AuClark/rave-cave/docs/visuals.md

# Generative visuals

Code-driven visuals you can reshape live, in the spirit of Zach Lieberman's sketches. A **sketch** is a small GPU shader with named parameters. The `visuals` service on the brain holds their live values, and any projector surface set to **generative** shows the sketch, warped to fit that surface. Code: [`brain/visuals/`](../brain/visuals/). Service: `visuals` on the brain, port **8110**.

## Using it

1. Open **`http://sektor5.local:8110/`** on a phone or laptop (on Android, use the IP: `http://<brain IP>:8110/`).
2. Move the sliders. The preview and every generative surface update as you drag.
3. **Q**, **W** and **E** are the same dice at three energies — calm, groove, full on for the drop. **Randomise** throws everything, **Nudge** moves each value a little, **Reset** returns to the defaults. Each group has its own **random** button.
4. **Save** a look as a preset and **Load** it later. Presets are per sketch, and carry the ranges and automation as well as the values.
5. In the mapping editor (`:8100/edit`), set a surface's content to **generative** to put the sketch on it.

Everything is beat-locked: speeds are in cycles per beat, and **Beat punch** sets how hard each beat kicks the visual.

**Two pages.** The **Launchpad** (`:8110/pad.html`) is the phone one: pads for energy, effects,
presets and a desk section, with a launch-on-the-beat quantise. The **full controls** (`:8110/`) are
for rigging a look up. They share the same state over the same event stream, so one device can set
up while another plays. Both are described in **[visuals-live.md](visuals-live.md)**.

**Live** (`:8110/show.html`) is the remote for the night: the lights and the visuals on one page,
with the track that's playing above the picture. See **[show-app.md](show-app.md)**.

**Playing it live — [visuals-live.md](visuals-live.md).** Every parameter has a **range** (the orange
band on its track, with two ▲ arrows) that everything else respects, and an **automation** toggle that
moves it between the ends of that range on its own, in note values, locked to the beat. There are
keyboard shortcuts for the lot. That guide is the one to hand someone who is about to VJ; what
follows here is the reference.

### What the page stores

| | |
|---|---|
| Values | `GET`/`POST` `/api/params`, as before: `{id: value}` |
| Themes and Shuffle | `sketches/themes.json` groups the sketches (a sketch not listed shows under Other). `GET /api/sketches` returns `themes` and `titles` with the names. `GET`/`POST` `/api/shuffle`: `{on, theme, every, skip, queue, out}`; `queue` is `{sketch, preset}` (or null to clear) for the next change, `out` is one theme's `{theme, sketches, presets: {sketch: [...]}}` left out of Shuffle, replaced whole; `every` is 1, 2, 4, 8, 16 or 32 bars; `skip` changes on the next 1. It runs in `visuals.py` on showbrain's beat (a 120 BPM idle clock with no deck), hands over through the transitions below synced to the bar so the change lands on the 1, and is saved in `state/shuffle.json`. Picking a sketch or preset by hand restarts the period |
| Ranges and automation | `GET`/`POST` `/api/auto`: `{id: {on, lo, hi, rate, shape, phase, retrig, hz, duty}}`, plus `_freeze` on POST to hold every automation where it stands |
| Presets | `{"_v": 2, "values": {...}, "auto": {...}}`. A preset written before automation existed is a flat `{id: value}` and still loads, with automation off and ranges wide open. |

The automation itself is worked out in [`render.js`](../brain/projector/web/render.js) (`autoEval`),
once per frame, from `u_beat` — so it is frame-exact on the projector, identical on every surface,
costs nothing on the network, and needs no shader recompile. The control page reads the same numbers
back out of the renderer to draw its moving markers.

### Marking a parameter in the JSON

Three optional fields, so the page does not have to guess from names:

| Field | Meaning |
|---|---|
| `"kind": "rate"` | This is a speed. The page snaps it to note values (1/32 … 8/1, dotted and triplet) and shows it as one. Stored in cycles per beat as everywhere else; negative is backwards and 0 is stopped. |
| `"kind": "quality"` | This buys frame rate, not looks. Randomise and Q/W/E leave it alone. `cathedral`'s Steps is marked this way. |
| `"kind": "fixed"` | This is identity, not a setting, so the dice leave it alone too. Rolling it does not give you a different look — it gives you something that is no longer the thing it is meant to be. `hypnotoad`'s collar, keyline and tint are marked this way (a Hypnotoad with a randomised collar is just a frog), and so are `wormhole`'s Two tone and Mirror. Two tone is a choice between black-on-white and colour, and a value half way between the two collapses the contrast between the card and the ink; Mirror decides whether half the words come out mirror-image, and rolling it means three rolls in four give you backwards type. Both are look decisions rather than energies, and both are the thing that sketch exists to protect. |
| `"energy": 1 / -1 / 0` | Which way this parameter pushes for Q/W/E: 1 = more of it is busier, -1 = calmer, 0 = neither, so just randomise it. Without the field the page uses a list of the usual movers and settlers. |

## Sketches

| Sketch | Controls |
|---|---|
| `rings` | Structure: ring count, spacing, inner radius, zoom. Shape: sides (3–12) and roundness (polygon to circle). Wave: frequency, amplitude, phase per ring, speed. Motion: twist per ring, spin, beat punch. Line: width, glow. Colour: hue, hue spread across the rings, saturation, follow the show's colour. |

| `field` | Elements: density (dots across the surface height, up to 60), size, size variation, round to square, filled to outline. Movement: wander, wander speed, drift speed and direction (the whole field travels across the surface). Wave: a travelling wave that swells the dots (amount, frequency, speed, direction). Links: lines to neighbouring dots (a moving net), link width, glow. Colour: hue, spread, colour by random or by the wave, saturation, follow the show's colour. |
| `eye` | The all-seeing eye for the capstone. Eye: size, open, opens through the build, wide open on the drop, blink, white of the eye. Iris: size, rings, fibres, pupil, dilate with energy, look around and its speed. Around: rays, ray length and spin, the dollar-bill triangle, glow, line width. Colour, a paper background and thin lines shooting from the pupil. |
| `sacred` | Gold line geometry. Mode 0 Sierpinski triangle zooming forever into its apex, 1 Flower of Life, 2 Metatron's Cube (Fill 0 = circles only, cheaper), 3 golden spiral (Fill adds the counter-spiral), 4 pyramid tunnel (Fill twists it). Scale, detail, zoom in cycles per beat, spin, a pulse that runs through the levels, width, glow, colour. |
| `ascend` | Energy climbing a pyramid face. With Triangle on, it clips itself to the face (apex top middle), so a plain surface over a face needs no masks. Edge light, capstone glow, charge level (climbs through a BUILD, full on the DROP), rising bands, glyph rows and their scroll, colour. |
| `subliminal` | They Live-style words. Mode 0 flash each bar, 1 strobe each beat, 2 steady, 3 hidden behind a bland broadcast until the DROP. First word and how many (0-8 the obey set: OBEY, CONSUME ...; 9-15 the wake-up set: WAKE UP, THEY LIVE ...), random order, hold, size, black on white, background flash, RGB glitch, jitter, grain. |
| `cctv` | A surveillance camera: night vision, thermal or grey; figures walking; a targeting box that jumps to a new one every few beats with a label; REC, camera number, timestamp and beat counter; grain, scanlines, rolling bar, vignette, glitch and zoom punch on the kick. |
| `redacted` | A classified document: black bars slide off on the beat to show glowing hidden words (MAJESTIC 12, MK ULTRA, AREA 51 ...). All revealed on the DROP, blacked out in the OUTRO. Lines, margin, scroll, dark paper, how much is redacted and revealed, how often, a stamp that thumps down each bar. |
| `cipher` | A wall of scrambling code, style 0 pigpen (the Freemasons' cipher), 1 binary rain, 2 numbers station, with a message in the middle row that decodes letter by letter every few bars, follows a BUILD, and completes on the DROP. |
| `area51` | Mode 0 radar with a beat-locked sweep and blips (one moves wrong), 1 a saucer whose tractor beam grows through the build and blazes on the drop, 2 a glowing crop circle. |
| `reptile` | Iridescent hex scales rippling on the beat, with a slit-pupil eye that blinks and opens wide on the drop. |
| `seething` | A lumpy ball of living cells (after Andy Lomas's Seething video). Size, grows through the section, lumps; cells across, jitter, seethe speed; Folds carves brain-like creases; shading, background (black to white), colour. |
| `seed` | Neon branching trees over glowing flower dots (after Vincent Houze's Seed video). Trees, levels, branch angle and shrink, sway, grows a level at a time through the section; width, glow, blossoms, ground flowers, colour from trunk to tips. |
| `orb` | A black glass orb with a pearl circling inside on vintage paper (after Whiskas fx's Harmonisch Serie video). Size, wobble, pearl size, orbit, gloss; paper, mirror into four or tile, RGB split on the kick, pearl tint. |
| `pipes` | White square pipes in a grey tiled room (after Graphset's Echoes Reality video). Cells, pipe width, density, round to square corners, one or two drifting layers, re-roll every few bars, shadows, room tiles, tint. |
| `wavelength` | Lines made of waves. Mode 0 ridgeline (stacked waveforms, each hiding the ones behind, like Unknown Pleasures), 1 flowing sine lines, 2 an oscilloscope trace with harmonics. Lines, amplitude, frequency, detail, ridge width, speed in cycles per beat, phase per line, width, glow, colour or a rainbow in the colours of visible light. Presets: unknown-pleasures, ridge-spectrum, ridge-gold, spectrum, moire, scope, scope-rgb. |
| `track` | The waveform of the song actually playing, from the decks. Mode 0 terrain (Unknown Pleasures made of the song: each ridge is a bar, the front one playing now, the bars to come rolling in, so drops are visible before they land), 1 scrolling colour waveform past a playhead, 2 ring (the current stretch round a circle with a sweeping hand), 3 bass/mids/highs meters. Bars shown, beats shown, playhead, brightness of what has played, height, contrast, width, glow, the track's own colours or a tint. Presets: terrain, terrain-gold, terrain-white, scroll, scroll-show, ring, meters. |
| `sisyphus` | Khepri meets Camus: a dung beetle, head down and hind legs up on the ball the way real ones push, rolls the sun up a hill it never gets to the top of. It walks backwards in an alternating tripod gait, feet planted on each push, and lurches uphill one stride per A loop. On the last bar of every climb (the last two, for climbs of 16 bars or more) the sun teeters, gets away, bowls the beetle over and rolls back down, and the next climb starts on the phrase. **The sun lights the sky**, so every climb goes night (stars) to dawn to day and every fall is a crash back to dusk, over a far dune with two pyramids. The sun's face goes from resigned to straining to wide-eyed as it falls. **Hand** is the medium, and it is marked fixed so the dice never switch it: 0 wax crayon (strokes at different angles per surface, colour past the lines, paper tooth), 1 1930s rubber-hose ink (the default: brush line of varying weight, yellowed colour, flicker, grain, dust and pale film scratches), 2 acid (rotating sunburst, op-art contour stripes, posterised neon), 3 pencil flipbook (graphite hatching on cream paper, the sun the only colour, every drawing held for a quarter beat so the motion steps on the beat). The sketch carries its own `drive()` on a held clock so the flipbook can freeze frames. Hill: slope, bars per climb, size, stride. Sky: how dark the foot of the hill gets. Hand: style, bars per style (when cycling), boil, ink, fade to sepia. Then the three reactive slots ([reactive.md](reactive.md)): **A Hit** the strides, the shove into the ball and the dust, **B Move** the sun's rays (alternate rays swap length on the 8ths), sparkle and star twinkle, **C Change** the sky's colour swell. Presets: cuphead (close-up), crayon, flipbook, acid, cycle, long-haul (a 64-bar climb in sepia), night-shift (red sun, steep, a fall every 4 bars). |
| `emergence` | A Turing-pattern labyrinth after Maxime Causeret's video for Max Cooper's *Order From Chaos*. Pattern: complexity, stripe density, spots to worms to fill, solid blobs. Motion: slither (cycles per beat), rewire, spin, beat punch (fattens the worms). Organism: size, hole, ragged edge, grow through the song section. Colour: zone mixing, hue shift, saturation, follow the show's colour. |
| `flow` | Particles streaming through a noise flow field, leaving fading trails, after [Radiant](https://github.com/pbakaus/radiant)'s Flow Field with Particle Trails by Paul Bakaus (MIT). Field: detail, curl, evolve per beat. Particles: density, speed in heights per beat, trail length, line width, width and alpha variation, quality (trace steps: fewer is cheaper on the projector's GPU). Beat: punch (brighter, thicker on the kick) and push (the streams bend away from the centre on the kick). Colour: hue, spread, saturation, brightness, background, follow the show's colour. Presets: amber, mono, blue, rose, emerald, arctic (the original's colour schemes), illuminati-gold, storm. |
| `topo` | A topographic contour map of slowly evolving terrain, after [Radiant](https://github.com/pbakaus/radiant)'s Topographic Contour Map by Paul Bakaus (MIT). Every 5th contour is major, with elevation labels on a dark knockout. Terrain: hill size, relief, evolve per beat. Contours: levels, line width, glow, scroll (levels per beat, so the rings march up or down the hills). Beat: punch, a peak in the middle (negative for a crater), its radius, swell on the kick. Labels: chance, size, spacing. Colour: the original coral → amber → gold ramp or a tint (hue, spread low to high, saturation), brightness, background, vignette, follow the show's colour. Presets: amber, mono, blue, rose, emerald, arctic, pyramid-peak, rave-rings. |
| `pendulum` | Pendulum Wave, after [Radiant](https://github.com/pbakaus/radiant)'s Pendulum Wave by Paul Bakaus (MIT). Pendulum i swings (base + i) times per cycle, so they drift from a line through snakes and braids and fall back into line at the end of every cycle; the cycle is in beats, so the line comes back on the phrase (128 beats = 32 bars). Pendulums: count, cycle, swings per cycle for the longest, swing angle, trail in beats. Look: size, the curve through the bobs, pivot bar and guides. Beat: bobs flash on the kick, a ripple from the centre on each beat. Colour: the original amber → gold → coral or a tint (hue, spread left to right, saturation), brightness, background, follow the show's colour. Presets: amber, mono, blue, rose, emerald, arctic, phrase-gold (16-bar cycle), neon-swing. |
| `phyllotaxis` | Phyllotaxis Spiral, after [Radiant](https://github.com/pbakaus/radiant)'s Phyllotaxis Spiral by Paul Bakaus (MIT): a sunflower of glowing points, each a golden angle round from the last, with a faint Fibonacci lattice between neighbours. A pixel finds the few points that can touch it by solving for its place in the local Fibonacci lattice, so thousands of points cost only nine lookups. Spiral: points, spacing, grow from the centre over a cycle of beats (oldest points fade from the middle, everything fades before it restarts). Motion: spin, breathing (point sizes, along the spiral), tilt sway, a ripple outward on each beat. Look: point size and glow, lattice lines, centre glow, vignette. Beat: flash on the kick. Colour: the original amber → gold → coral along the spiral or a tint, brightness, background, follow the show's colour. Presets: amber, mono, blue, rose, emerald, arctic, golden-sunflower, vortex. |
| `sequin` | Sequin Wave, after [Radiant](https://github.com/pbakaus/radiant)'s Sequin Wave by Paul Bakaus (MIT): tiny mirror sequins on a hex grid, tilted by five interfering waves, flashing copper → gold → white as they catch the light. Ported nearly line for line (its reversed smoothsteps rewritten, since they're undefined in GLSL). Sequins: how many across, wave speed per beat, tilt, sparkle, individual shimmer. Beat: sparkle on the kick, a ring of flashes running out from the centre on each beat. Light: a roaming light (the original's mouse light) circling the surface, laps per 16 beats. Colour: the original gold or a tint, brightness, vignette, follow the show's colour. Presets: gold, silver, rose-gold, sapphire, emerald, disco-gold, dancefloor. |
| `gilt` | Gilt Mosaic, after [Radiant](https://github.com/pbakaus/radiant)'s Gilt Mosaic by Paul Bakaus (MIT): a Byzantine gold mosaic wall lit by three drifting candle lights, its tesserae turning over in a wave. Ported nearly line for line (reversed smoothsteps rewritten; its hash() is the renderer's). Mosaic: tiles per height, candlelight drift per beat, tile shimmer. Flip: wave on or off (off gives the still, shimmering wall), sweep and rest in beats (6 + 2 = one sweep every 2 bars), direction, a radial flip from the centre every N beats (the original's click). Beat: the gold flares on the kick. Colour: the original gold or a tint, brightness, vignette, follow the show's colour. Presets: byzantine, candlelit, silver-leaf, rose-gold, lapis, temple-drop, neon-temple. |
| `throne` | Golden Throne, after [Radiant](https://github.com/pbakaus/radiant)'s Golden Throne by Paul Bakaus (MIT): a golden sacred-geometry mandala of rings, petals, spokes, hexagons and triangles in counter-rotating layers, with golden-ratio spiral arms and fractal hex lace. Ported nearly line for line (reversed smoothsteps rewritten, and the original's spokes fixed: they drew dark rays through the mandala). Mandala: size, layers, spiral arms, lace. Motion: time per beat, layer rotation, whole spin. Beat: the lines glow and the centre flares on the kick. Colour: line glow, the original gold or a tint, brightness, follow the show's colour. Presets: golden-throne, cathedral, platinum, rose-window, lapis, ascension, portal. |
| `geometry` | Radiant Geometry, after [Radiant](https://github.com/pbakaus/radiant)'s Radiant Geometry by Paul Bakaus (MIT): golden sacred geometry that morphs from a tiled hex lattice of star rosettes to a single central mandala with petals, spiral arms and an ornate edge. Ported nearly line for line (reversed smoothsteps rewritten). Pattern: the morph (lattice → mandala), a swing toward the mandala over a cycle of beats, build through the song section (lattice early in a section, mandala by its end, so it forms through a BUILD), complexity (2 to 6 layers), size. Motion: time per beat, layer rotation, whole spin. Beat: the lines glow and the centre flares on the kick. Colour: line glow, the original gold or a tint, brightness, follow the show's colour. Presets: lattice, girih, mandala, breathing-temple (swings every 8 bars), build-to-mandala, platinum, neon-girih. |
| `tropical` | Tropical Heat, after [Radiant](https://github.com/pbakaus/radiant)'s Tropical Heat by Paul Bakaus (MIT): heat haze and chromatic aberration over flowing domain-warped noise in hot magenta, orange, amber and teal, with blooms of vivid colour. Ported nearly line for line (reversed smoothsteps rewritten). Heat: distortion, colour vibrancy, time per beat, zoom. Beat: the blooms flare on the kick; heat can follow the track's energy. Colour: hue shift, shift by the show's colour, brightness, vignette. Quality: octaves (the original's 6 is the heaviest sketch here) and chromatic mode: full samples the noise three times, once per colour channel, which is the original's fine, busy look; off (the default) samples once and shifts red and blue, a smoother liquid flow at about a third of the cost. Presets: tropical-heat (exactly the original), lite (cheapest), heatwave, lagoon, ultraviolet, carnival. |
| `eclipse` | A solar eclipse, played out: the moon crosses a limb-darkened sun over a cycle of beats, from a bite and a crescent through Baily's beads (sunlight through the valleys on the moon's limb) and the diamond ring into totality with the corona, chromosphere and pink prominences, then back out. The corona, solar wind, bloom and stars are from [Radiant](https://github.com/pbakaus/radiant)'s Eclipse Glow by Paul Bakaus (MIT; reversed smoothsteps rewritten, its hash renamed, stars and grain sized in output pixels). Eclipse: crossing in beats (0 = set the phase by hand; 0.5 is totality), how much of the cycle totality holds, totality as each song section ends (so a BUILD lands on totality), the moon's path angle, a miss (a partial eclipse), moon size (under 1 gives an annular ring of fire, with no corona), size. Sun: brightness, corona size, rays, prominences, lens streak, stars, corona time per beat. Beat: the corona and diamond ring flare on the kick; diamond strength. Colour: hue shift, shift by the show's colour, brightness. Presets: crossing, totality, diamond-ring, build-to-totality, ring-of-fire, partial, great-corona, blood-moon, black-sun. |
| `diamond` | Diamond Caustics, after [Radiant](https://github.com/pbakaus/radiant)'s Diamond Caustics by Paul Bakaus (MIT): prismatic fire through a brilliant-cut diamond, with caustic folds from faceted refraction, chromatic dispersion into rainbow fire, scintillating sparkles and star bursts. Ported nearly line for line (17 reversed smoothsteps rewritten, its hash and a local named refract renamed, float loops made int, and a seam in the original's dispersion fixed). Diamond: brilliance, fire (dispersion), sparkles, star bursts, zoom. Motion: time per beat, turning. Beat: sparkles and star bursts flash on the kick. Colour: hue shift, shift by the show's colour, brightness (default 0.55: the original's exposure washes out; the original-exposure preset has it). Heavy: about ten caustic lookups per pixel. Presets: brilliant, fire, ice, disco-diamond, sapphire, ruby, rave-rock, original-exposure. |
| `umbrella` | Rain on Umbrella, after [Radiant](https://github.com/pbakaus/radiant)'s Rain on Umbrella by Paul Bakaus (MIT): looking up through a rain-soaked umbrella at a blurred night city. The original simulates drops on a canvas every frame and hands them to a refraction shader; this is a stateless rebuild of the look: drops land (on the beat if you like), sit, then slide down the dome leaving trails of droplets, each one a lens onto a sharper, displaced piece of the city bokeh, with micro-droplets beading and drying between. The ribs, panels and hub are the original's shader code. Rain: amount, drop size, drop life in beats, slide, trails, micro-droplets, impacts on the beat. Look: refraction, city blur, city lights, walk (the city drifts past), umbrella ribs. Beat: the lights pulse on the kick. Colour: hue shift, shift by the show's colour, brightness. Presets: night-walk, downpour, drizzle, standing-still, neon-blue, rave-rain. |
| `artpop` | Artpop Iridescence, after [Radiant](https://github.com/pbakaus/radiant)'s Artpop Iridescence by Paul Bakaus (MIT): iridescent soap-film bubbles, thin-film rainbow bands over a domain-warped surface with fresnel edge glow and chrome highlights. Ported nearly line for line (reversed smoothsteps rewritten; the bubble edges' atan noise, which seamed at ±π, sampled round a circle instead; the small bubbles only computed where they are). Film: thickness (how many bands), flow per beat, warp (1 = the original, which folds the film into fine grain), size, small bubbles on or off, chrome highlights. Beat: the bands shimmer and the bubbles swell on the kick. Colour: band shift, shift by the show's colour, brightness. Quality: octaves (the original's 4 with full warp is about 190 noise lookups per pixel; the default 2 octaves at 0.4 warp is clean and about half that). Presets: holographic, original, lite, oil-slick, chrome-bubble, single-bubble, holo-pop. |
| `horizon` | Event Horizon, after [Radiant](https://github.com/pbakaus/radiant)'s Event Horizon by Paul Bakaus (MIT): a ray-traced Schwarzschild black hole. Each pixel follows its light ray's bent path (velocity-Verlet geodesics), crossing a Novikov-Thorne accretion disk with Doppler beaming and gravitational redshift, so the far side of the disk arcs over the shadow, with a photon ring and a lensed star field. Ported nearly line for line (its hash renamed). Black hole: zoom, disk brightness, chromatic (spectral rings), photon ring fringe, stars. Camera: orbit in turns per 64 beats, tilt (-0.2 gives the edge-on Interstellar view), roll, disk spin per beat. Beat: the disk flares and the photon ring pulses on the kick. Quality: step (1 = the original's up to 200 steps per pixel, the heaviest sketch here; the default 1.5 looks the same at two-thirds the cost). Presets: event-horizon, gargantua (original steps), lite, spectral, edge-on, from-above, singularity. |
| `burn` | Burning Film, after [Radiant](https://github.com/pbakaus/radiant)'s Burning Film by Paul Bakaus (MIT): celluloid catching fire in a projector. Burn holes open in dark film stock with a white-hot frontier and spread until it's all fire, embers glowing through, sparks drifting up, sprocket holes and grain; then it fades to black and a fresh strip starts. Ported nearly line for line (its many reversed smoothsteps rewritten, noise renamed, loop made int, grain sized in output pixels, and its sprocket holes, which came out as flat dashes, redrawn as real rounded holes). Burn: direction (spread, the default, or die down: the original's fire actually shrinks over its cycle, the opposite of what it describes), cycle in beats, burn through the song section (the film burns away over a BUILD, all fire by the drop), pattern drift, burn size. Fire: burning edge, ember glow, sparks. Film: sprocket holes, film run (the holes scroll through the gate, in holes per beat), grain. Beat: the frontier flares on the kick. Colour: hue shift, shift by the show's colour, brightness. Quality: octaves (6 = the original). Presets: burning-film, original, burn-the-build, fast-burn, slow-burn, blue-flame, toxic. |
| `vertigo` | Vertigo, after [Radiant](https://github.com/pbakaus/radiant)'s Vertigo by Paul Bakaus (MIT): an endless crimson tunnel of neon rings and segments, lit by waves of light running along it, with sparse ring flashes. Ported nearly line for line (reversed smoothsteps rewritten; its hash is the renderer's; its unused Spiral Intensity now twists the tunnel). Tunnel: speed in rings per beat, spiral, spin in turns per 64 beats, ring density, segments round. Light: wave speed, ring flashes, neon edges. Beat: the rings flash on the kick. Colour: hue shift, shift by the show's colour, brightness. Presets: vertigo, hyperdrive, spiral-down, ice-tunnel, acid, rave-tunnel. |
| `silk` | Silk Cascade, after [Radiant](https://github.com/pbakaus/radiant)'s Silk Cascade by Paul Bakaus (MIT): three layers of translucent silk in gold, rose and lavender, with domain-warped folds, Kajiya-Kay anisotropic sheen, backlit peaks and rare sparkles, drifting at different depths. Ported nearly line for line; the sheen's pinch points (where a fold flattens and its tangent is undefined) are faded out, and since the original's sheen is near full almost everywhere and washes the image out, sheen defaults to 0.7 with a contrast control (the original preset has both at 1). Silk: flow per beat, sheen, contrast, fold size, layers (1 to 3), sparkles. Light: the key light's orbit in turns per 64 beats. Beat: the sheen flashes on the kick. Colour: hue shift, shift by the show's colour, brightness. Presets: silk-cascade, original, emerald-silk, crimson-silk, single-sheet, disco-silk, show-silk. |
| `milking` | Alien Dairy: two greys milking a dancing cow under their saucer in a moonlit field, a cartoon drawn from 2D distance fields with ink outlines. The cow bobs, sways, stamps its legs in pairs, head-bops, swishes its tail and jingles its bell on the beat; the greys take turns, one squirt per beat, into a bucket that fills over a cycle of beats; the saucer's rim lights chase and its tractor beam flickers on the kick. Scene: dance, size, bucket fill in beats, ink line. Saucer: tractor beam, rim lights, beam hue, beam follows the show's colour. Night: stars, moon, brightness. Beat: the beam flares on the kick. Presets: moonlight-dairy, disco-dairy, slow-moo, red-alert. |
| `atlantis` | Atlantis Rising: Moses parts the sea and finds Atlantis, overrun by dolphins with thumbs. A cartoon drawn from 2D distance fields with ink outlines. The walls of water (foam, currents, spray) part over a cycle of beats, hold, then crash shut, or part through the song section so they're fully open by the drop; Moses raises his staff on every beat, its tip glowing; the temple, towers and crystal spire of Atlantis sit on the seabed, the crystal pulsing on the kick and throwing rays up between the walls; dolphins leap across the gap in their own lanes, each giving a thumbs up that pumps on the kick. The sea: part-and-close cycle in beats (0 = by hand), parted by hand, part through the section. Dolphins: how many, thumb size. Atlantis: crystal glow, light rays, glow hue, glow follows the show's colour. Look: size, ink line, brightness. Beat: the crystal and thumbs on the kick. Presets: parting, part-the-build, dolphin-party, red-sea-rave, exodus. |
| `wormhole` | **Your own words**, running round the inside of a pipe you are falling down. Type them on the Visuals page (or the pad's drawer) and separate them with `|`, up to eight. Two changes of coordinates stacked. Take the log of the radius and you get a distance that never runs out, so stepping it by whole numbers gives ring after identical ring with no end and no seam, and the angle is somewhere to run text along; travel and spin are then one term each, in cycles per beat, and every ring down to the vanishing point costs the same as the first. Before that the plane goes through a **Möbius transform**, `(z − a)/(1 − conj(a)·z)`, which maps circles to circles but moves the centre: the rings come out nested and not concentric, and the vanishing point sits off to one side at `a`. Because the map is conformal the letterforms stay letterforms, and its Jacobian keeps each ring's hairline one pixel wide. **It is lit.** How far down the pipe a ring sits drives the fog, so near words are bright and far ones sink into darkness towards a hot core at the vanishing point; the wall is a dark tint of the show hue and each word takes a hue either side of it (Follow is on by default, so Hue is an offset). Near letters have their edges sharpened back to a pixel, and far ones too small to read fade out instead of shimmering. **Two tone** (fixed) is the print version: black type on card, depth as haze, the pulse as a thickening hairline. **The sliders are scaled for reading, not for range**: every min and max is where the words still read, so a randomise, **Drop** included, gives a different tunnel and not an unreadable one. **Twist counts whole rings gained per turn**, and it has to be whole: `atan` has a branch cut at ±π, so a fractional twist makes the ring coordinate jump where the angle wraps and cuts the letters in half; it doubles as how many words are in the cycle. **Mirror** (fixed) folds the angle into wedges; half the words come out mirror-image, which is what a kaleidoscope does to type. Pipe: vanishing point off centre and its wander, rings per turn, times round, ring fill, travel, the kick's lurch, spin, twist, counter-creep, mirror. Type: seam hairline, weight, outline, Hectic (how much the hit brings in the streaks, chromatic split and bloom). Effects: those three always-on. Light and depth: fog (darkness gathering down the pipe), core glow, the kick's ring of light, hats glint, ribs, vignette. Then the three reactive slots ([reactive.md](reactive.md)): **A Hit** (every beat by default) lurches you down the pipe (forward only, beat-locked), fires a ring of light out of the hole and flares the core, **B Move** wanders the vanishing point and turns the pipe, **C Change** swaps the words and the palette. The hats glint the seams through their own `hats` amount, outside the slots, so kick, hats and chords each do something different without re-routing. Presets: hyperspace (a three-word spiral), kaleido, night-print, panter, read-me, strobe-words, event-horizon (warm, deep fog, a blazing core). None carries text, so they keep whatever words are typed. |
| `hypnotoad` | ALL GLORY TO THE HYPNOTOAD. Front-on and symmetrical in his own olive and cream whatever the show hue is doing (Tint overrules that), and **the eyes are the point**: bulging yellow eyeballs, shaded round with a glassy highlight and cupped by a lower lid, whose irises fill most of the eye and pour concentric bands of colour out of a small black pupil without stopping. The bands move in rings per beat with most of each beat's travel just after the kick; negative pours them inward. On the kick the iris widens and the pupil shrinks, a pale ring shoots outward through it and the eyes glow. Iris colour: 0 fire (pale yellow, orange, red, crimson), 1 rainbow, 2 the background's hue. The blink is an olive lid sweeping down. Behind him wavy hypno rings radiate from his eyes rather than the middle of the screen, on a small quantised palette with near-black dark bands (default violet, which makes the olive and the fire eyes pop), under **sacred geometry** with a soft glow, faded behind him so it frames him instead of crossing his face (0 Flower of Life, 1 Metatron's Cube, drawn from 11 lines by its hexagonal symmetry, 2 a ring-and-spoke mandala). **Caption** (fixed) puts ALL GLORY TO along the top and THE HYPNOTOAD along the bottom, meme-poster style, flashing on the kick, and he shrinks to fit between them. He is kept in frame: drawn big he crops at the feet, never the eyes. Toad: size, bob, blink, blotches, tint, collar, line weight (the last three fixed). Eyes: size, pupil, iris rings, how fast they pour, iris colour, caption. Then the three reactive slots ([reactive.md](reactive.md)): **A Hit** the bob and the eyes, **B Move** the geometry turning and the rings wobbling, **C Change** the palette and the line-work. Presets: glory (caption on), obey, stare, strobe-toad, swamp, temple, inward (rings pouring inward, rainbow irises). |
| `labyrinth` | A first-person walk through a maze that never ends, and it gives hope. You step a cell a beat (lurching on the kick, with a footfall dip and sway) and turn on the downbeat, the head easing into each corner. **The route is a pure function of the beat** and can never cross itself: it only ever gains ground one way, as straights and one-cell jogs with closed forms, so there is no state and every projector draws the same frame. The walls come from the route plus hashed side openings, alcoves, dead ends and colonnaded halls, and the route is never shut. **Drawn by an exact grid walk through the cells**, floor and roof as planes and encounters as analytic shapes, with no marching; on SwiftShader every branch runs, so the worlds are data rather than branches and each pixel draws one encounter. **Hope** is the subject: a lamp always waits round the next corner, growing and throwing rays down the corridor as you approach, then moving on as you take the turn; Ariadne's thread glows down the floor and round every corner with a bead of light running ahead on the kick; fireflies drift towards the light; and at the end of every phrase the roof slides open a panel at a time, light pours down in columns, and it closes on the next downbeat (it also opens on a drop). **Encounters** every few bars, seen coming down the straight and reached on a downbeat: glowing mushrooms you eat (a bloom, a shockwave down the corridor, then the maze trips for a phrase), a lantern, an orb, a door of light, a portcullis that lifts on the kicks, a curtain of threads, a fallen pillar. **World** (fixed): 0 hedge maze at dusk, 1 torchlit stone labyrinth, 2 neon grid under a synthwave sun, 3 ink on paper, 4 the mushroom trip. Walk: pace, bars per turn, lurch, bob, sway, field of view. Maze: world, branching, wall height, thickness, texture. Hope: the light ahead, thread, fireflies, fog, sky, how often the roof opens. Encounters: how often, which kinds (anything, mushrooms, lights, obstacles, lights and obstacles), how hard the trip. Render: steps and depth (frame-rate knobs). Then the three reactive slots ([reactive.md](reactive.md)): **A Hit** the footfall and the lamps, thread and fireflies flaring, **B Move** firefly sparkle, torch flicker, thread sway and a glance aside, **C Change** the light ahead swelling and the palette. Presets: minotaur, long-way-home, catacomb (stone), dusk-garden, magic-mushrooms (hedge), gridrunner (neon), sketchbook (paper), the-trip. |
| `mouths` | One huge mouth fills the screen and acts: fourteen exaggerated emotions (grin, smirk, a sinister Cheshire grin, a yell down to the uvula, a belly laugh, a gasp, a grimace, a pout, tongue out, a lip bite, a snarl over one canine, belting, a nervous anime wobble, and **bass face**). **A rig, not drawings**: every emotion is 24 numbers (open, width, each corner up or down, sneer each side, which teeth and gums show, clench, tongue, pout, lip bite, menace...), and the mouth springs from one to the next with overshoot and a stretch while it moves, starting just before the 1, so it never cuts. The lips are four curves across the width; the teeth are individual, with gaps, canines and gum scallops; the inside has a throat, uvula and a grooved tongue. **Bass face is tied to the track**: it fires hardest when the bass comes back in (how hard the kick lands at the beat onsets now against eight beats ago, calibrated on a real rekordbox waveform: onsets about 0.73 through heavy sections, 0.26 in breakdowns), simmers while it stays heavy, and takes over on the drop; the jaw pump turns into a head nod under it. Dancing: the jaw drops on the kick, the opening follows the mids, and the hats flick consonant shapes (M, F, O, E) on the 8ths. **Style** (fixed): 0 anime (clean line, cel shading, a fang, sweat drops and anger marks), 1 cartoon (thick ink), 2 detailed (shaded enamel, gums, a wet tongue, saliva strings), 3 pop art (halftone). Mouth: size, exaggeration, elastic, face hints, fang. Emotion: how often it changes (or hold one), which, mood (a family of emotions: happy, gremlin, cheeky, diva, anime chaos, sinister, stank), bass, drop. Dance: pump, sync, talk, bob. Style: style, ink, gloss, spit. Background: burst, halftone, speed lines, flat pulse or the style's own, and how busy. Then the three reactive slots ([reactive.md](reactive.md)). Presets: gremlin, diva, stank (mostly bass face), anime-chaos, pop-art, cheshire (slow and sinister), cheeky. |
| `inkwell` | Rubber-hose cartoons, after Fleischer, early Disney and Cuphead, climbing up out of an ink pool down a log-polar tunnel, or dancing in a row along a stage. Twelve subjects (a mascot critter, teapot, tree, flower, alarm clock, toadstool, cactus, ice cream, bomb, 1930s radio, candle, ghost) on **one shared rig**: pie-cut eyes and quick blinks, a grin that opens on the kick, noodle arms in white four-finger gloves, noodle legs down to big round shoes. **The feet stay planted and the body bobs over them**, so the legs bow like rubber; it squashes wide on the beat (harder on a loud kick), stretches on the way up, and rocks and shimmies a step behind its neighbour, with arm poses (charleston, hands up, elbows out) changing every 4 bars. The ink is thick and scales with the character, with a finer pen for faces and gloves, and **boils** four times a beat; halftone shades the side away from the light. The bodies are **masks** filled with a pattern drawn in their own coordinates, so it travels and squashes with the shape: 0 checkers, 1 candy stripes spiralling in, 2 polka dots, 3 op rings. **Colour is one of eight designed palettes**, each with its own card, floor, three fills, pattern and limb colour: 0 inkwell, 1 sunday comic, 2 silent, 3 neon, 4 two-strip, 5 hellfire, 6 seaside, 7 acid. Hue rotates the palette, Spread says how often a character reshuffles which colour goes where, and a continuous rainbow is deliberately not on offer: it is the single thing that makes work like this read as a screensaver. **Layout** 1 is the tunnel: every ring is a floor with an ink line under the feet and the wedges alternate colour, and Spin and Zoom are one term each (negative Zoom climbs out of the pool). Layout 0 is a chorus line on a stage, in front of a title-card sunburst. Small characters far down the tunnel drop fingers, props and faces, which is most of why it got cheaper. Cast: layout, how many, bars per subject, size, bounce, dance, how many get limbs. Movement: spin, zoom. Pen: line, boil, noodle. Fill: amount, pattern, scale, travel, halftone. Faces and props: strength, how many, how much C brings them in. Scene: background tint, rosette, background, film. Then the three reactive slots ([reactive.md](reactive.md)): **A Hit** the bounce, squash, eyes and mouths (and the candle flame, radio speaker and bomb spark), **B Move** noodling hoses, wiggling fingers and blinks, **C Change** the fills swelling and turning and who the cast reaches for next. Presets: tunnel, sunday-comic (row, polka dots, heavy halftone), silent (row, greys, heavy film), chorus (row, two-strip), deep (neon, op rings), warp (hellfire, deliberately chaotic), they-blink (acid, the faces arrive on the chords). |
| `cathedral` | A gothic nave you fly down and never reach the end of. Built from simple shapes so the architecture reads: a polished marble floor, fluted clustered piers rising into a pointed rib vault (diagonal and ridge ribs), pointed arcades opening onto dark side aisles with their own glowing windows, stone laid in visible courses, and above the arcade a great window in every bay whose **tracery is the fractal**: each arch holds two smaller arches and a round window, and each of those the same again, mirrored about the centre line, which is how real gothic windows are drawn. **Light is the subject**: a rose window at the far end throws beams back down the nave, sun shafts slant through the left-hand glass and pool on the floor, and the haze brightens towards the window so distance glows rather than going murky, with the near stone dark against it (projectors wash out mid-darks). The glass follows the show hue (Hue is an offset; Spread sets how many colours). **Raymarched**: the floor is hit exactly rather than marched, everything else is cheap to test per step, and the tracery, glass and rose are only worked out on the pixels that land on them. **Kaleidoscope** (`kal`, 0 = off, the default) folds the screen angle into mirrored wedges before the march, so neighbouring wedges meet in reflection, never a jump, and Roll turns the building inside them like a real kaleidoscope; narrow wedges are turned towards the side windows so each always holds glass. Structure: rose petals, tracery generations, tracery scale, form, fold, nave width, height. Flight: beats per bay, the kick's surge forward, the nave winding side to side (Twist; a true corkscrew would break the exact floor), roll, sway, kaleidoscope. Render: steps (the one frame-rate knob), depth, haze, shafts and beams, rose size, shading. Then the three reactive slots ([reactive.md](reactive.md)): **A Hit** surges you forward (continuous, never jumping back) and flares the rose, haze, glass and shafts with a wave of light up the nave, **B Move** makes the glass glitter pane by pane, **C Change** turns the glass palette and breathes the tracery's round windows. Presets: plain nave: nave, gold-vault, rose-window, cavern (a low, wide, red crypt), strobe-hall, lean; kaleidoscope: crystal (six-point star tunnel), hyperdrive (three wedges, fast, winding, rolling), rose-kaleido (twin rose windows in an eye). |

Low sides with no roundness, zero wave frequency and some twist gives the stacked, rotating-polygon spirograph look. High frequency with small amplitude gives rippling contour lines. In `field`, turning up Links with some Wander gives a drifting net; Wave with no Wander gives a clean grid of dots swelling in bands. In `emergence`, a large Size with no Hole fills the surface with maze (good for walls), and low Spots → worms gives cells instead of worms.

`emergence` is not a real reaction-diffusion simulation (that needs a feedback buffer the renderer doesn't have yet). It adds up plane waves of one wavelength in scattered directions and colours where the sum is above a level, which gives the same labyrinth with no memory between frames, so every surface stays in sync.

### Parameters that can empty the picture

The rule is that nothing may ever blank the screen, and the ranges are always clamped to each
parameter's own min and max, so automation cannot take a value somewhere the sketch does not allow.
Within that, these are the ones to be careful of when setting a range by hand:

| Sketch | Parameter | At its extreme |
|---|---|---|
| any reactive | `aamt` `bamt` `camt` at 0 | Not blank, but nothing reacts — the picture goes static |
| `cathedral` | `far` at its lowest | The nave ends in haze sooner; the near bays and their glass still draw |
| `cathedral` | `fog`, `glow`, `shade`, `sat` all at their lowest | The darkest it goes: flat stone, but the glass still reads clearly |
| `inkwell` | `bg` at 0 | The card goes black; the cast still draws, so it reads rather than disappears |
| `inkwell` | `size` at its lowest | The cast shrinks towards specks |
| `inkwell` | `pat` 0 **and** `face` 0 | Legal and fine — flat colour shapes — but the least interesting thing the sketch does |
| `inkwell` | `bg` 1 on a light palette | The card washes to near-white; the characters still read |
| `wormhole` | `fog` at its highest | The far rings sink into darkness sooner, but the near ones and the core always show. (Fog used to be an inverse radius, `0.07 / fog`, which blanked the card at its low end; it is now plain depth, 0–1.) |
| `wormhole` | `rings` at its lowest with `reps` 1 | Huge letters, a half-word per ring; still legible, which is why the floor is 1.8 |
| `subliminal` `redacted` | `bg` / paper values | Can go to solid black between flashes, which is the intent |

`cathedral`'s fold angle was the one real offender and is no longer reachable: the slider is mapped
onto the window that always builds something (see [reactive.md](reactive.md#gotcha-a-driver-must-not-be-able-to-empty-the-picture)).

### What the heavy sketches cost

Measured on the CPU rasteriser here (SwiftShader) at 1280×720 as a ratio to `rings`, medians of
interleaved runs on a busy machine. Only the ratios mean anything, and none of this was measured on
the projector's own GPU. After the rework:

| Sketch | vs `rings` | Before |
|---|---|---|
| `wormhole` | about 1.5× | 1.25× |
| `inkwell` | about 2.3× (`deep` 2.6×) | 2.9–4× |
| `hypnotoad` | about 2.3× | 2.2× |
| `sisyphus` | about 2.8× | 3.0× |
| `cathedral` | about 2.8× (`hyperdrive` 3.1×) | 5.9–6.6× |
| `labyrinth` | about 2.7× (`magic-mushrooms` 2.95×) | new |
| `mouths` | about 1.8× | new |

`cathedral` is the only sketch that raymarches, walking a ray through the scene for every pixel
where every other sketch answers each pixel with a formula. It halved when the 3D fold fractal
went: the floor is now hit exactly, the rest of the scene is cheap to test at each step, and the
glass is only worked out where it shows. **Steps** barely changes the cost any more (24, 48 and 96
are nearly the same); **Depth** shortens rays that hit nothing, and the sun shafts are about an
eighth of it. SwiftShader runs every branch, so the early-outs in `sisyphus` and `inkwell` show
nothing here and should pay on a real GPU. **Put the heavy ones on the rig and watch the fps on the
projector's stats before they go in a set.**

Each generative surface is drawn separately, so putting `cathedral` on two surfaces costs twice,
and the Stage page draws it again on top of the projector's own copy.

## Transitions

Changing the sketch, or loading a preset, hands over on the projector through a transition in time with the music, set in the **Transitions** section of the control page. The old sketch stays up until the sync point (now, or the next beat, bar or 4-bar phrase, or landing on the next drop), then the two play together for the transition's length in beats.

| Type | What it does |
|---|---|
| Auto (smart) | Picks one that suits the song section showbrain is in, never the same twice running: a flash cut, a stutter or a zoom into a PREDROP or DROP; a zoom, swirl, pixelate or tiles through a BUILD (1 bar); a dissolve, luma, crossfade or iris in a BREAKDOWN, INTRO or OUTRO (4 bars); a wipe, iris, tiles, slices, dissolve, pixelate or swirl in the groove. |
| Cut | An instant change on the sync point. |
| Crossfade | A straight fade. |
| Wipe | A soft line sweeps across at one of 8 angles, lit in the show's colour. |
| Iris | A glowing circle opens from the centre. |
| Dissolve | The new sketch burns through the old in noise-shaped holes with a hot edge. |
| Luma | The new sketch's bright parts appear first, then its darks. |
| Tiles | Squares pop in at random, each growing from its centre. |
| Glitch slices | Horizontal bands of the new sketch slide in from the sides. |
| Zoom through | The old sketch zooms in and away while the new one flies in from the centre as a framed picture. |
| Swirl | The old one twists away as the new one untwists in. |
| Stutter | The two flicker on 16th notes, the new one more and more, until it holds. |
| Flash cut | A white flash, with the cut on its peak. |
| Pixelate | The old one breaks into big pixels and the new one resolves out of them. |
| None | Instant, as before. |

Length is automatic (each type's own) or 1 beat to 8 bars. **Presets morph too** makes loading a preset transition from the old values to the new ones in the same sketch. **Mix to the next one** switches through the current transition to what Shuffle would pick next: Next up if something is queued, otherwise a sketch from Shuffle's theme with one of its presets, only from what is ticked in (see Themes and Shuffle). It works with Shuffle off. **Shuffle's own changes go through transitions too**: it sends each one inside the last beat of the bar with the sync forced to the bar, so every projector starts it exactly on the downbeat however late the message arrives, and the transition is never longer than Shuffle's period (an instant change becomes a cut on the 1). The API is `GET/POST /api/transition` (`type`, `beats`, `sync`, `presets`), `POST /api/next`, and `POST /api/select` takes an optional `"transition": {...}` to override the settings once (e.g. `{"type": "cut"}`).

How it's drawn: while a transition runs, each generative surface draws the outgoing sketch with its old values and then the incoming one on top, whose alpha is the transition's mask (in `render.js`, `COMMON`: `u_trole`, `u_tp`, `u_tmode`, and the `s5t_` functions). Either side can warp its own coordinates (zoom, swirl, pixelate, slices). There's no render-to-texture, so it runs on the projector's WebGL1 GPU, but for the transition's length the surface costs both sketches together: going between two heavy sketches (tropical, diamond, artpop, horizon) may stutter on the X3. Sketches need no changes.

## Climaxes on the drop

Timeline sketches have a best moment: eclipse's diamond ring into totality, atlantis's sea fully parted, burn's frame all fire, pendulum's bobs back in one line, geometry's full mandala, milking's full bucket, phyllotaxis's full bloom. Left alone, their cycles run on the beat count and the climax lands wherever it happens to. showbrain predicts the next drop from the track's analysis (`beats_to_drop`), so these sketches can aim for it: with **Land the climax on the drop** on (in their Beat group, on by default), the renderer eases the sketch's cycle, running it up to twice as fast or holding it, so the climax arrives on the drop's downbeat, getting there about a bar early. With no drop predicted (no rekordbox analysis, or none coming) the cycle runs on from wherever it is, so it never jumps. The kick and other beat animation stay on the real beat; only the cycle is moved.

A sketch opts in with a `climax` entry in its JSON: `{"cycle": the param holding its cycle length in beats, "peak": where the climax is in the cycle (0..1, or an expression of its params such as "0.5 - hold / 2"), "lock": the on/off param, "what": a description}`, and runs its cycle on `u_cbeat` instead of `u_beat` (see `MapRenderer._cbeat`). Sketches also get `u_todrop` (beats to the predicted drop, -1 when none) and `dropArc()` in the shared header: 0 far from a drop, rising to 1 over the 16 beats before one and easing off over the 8 after, for anything that should build into the drop.

Transitions can land on the drop too: set the Transitions sync to **Land on the next drop** and the change's cut (its end, or a flash cut's peak) falls on the drop's downbeat, shortened to fit if the drop is close; with no drop predicted it waits for the next bar. Auto does this by itself when the change comes in a BUILD, HOLD or PREDROP with a drop predicted within 16 bars.

## Writing a sketch

Add two files to `brain/visuals/sketches/`:

- **`NAME.glsl`**: declares `uniform float p_<id>;` for each parameter and defines `vec3 content(vec2 uv)`. `uv` is 0..1 across the surface. It can use everything the projector's shaders get: `u_beat`, `u_frac`, `kick()` (1 on the beat, decaying), `u_hue`, `u_energy`, `u_scene`, `u_aspect`, `hsv()`, `hash()`, `wave(beat)` (the live track's waveform, see below), and `drive()` with `band()`, `loopBeats()` and `barBeat()` (see [reactive.md](reactive.md)). See [`render.js`](../brain/projector/web/render.js) (`COMMON`).
- **`NAME.json`**: title, description and parameter groups, each parameter with `id`, `label`, `min`, `max`, `step` and `default`. The control page builds its sliders from this.

Deploy with `brain/deploy.sh visuals` and pick it in the Sketch card on the control page. If the shader doesn't compile, the control page shows the error and the projector keeps the last working sketch.

For sketches driven by the track's frequency bands on their own loop lengths — the kick punching on the beat, the hats in 8ths, the chords swelling over 8 bars — see [reactive.md](reactive.md). Every sketch already has `drive()`; `sisyphus` is the one built on it.

## Conspiracy set

Sketches and presets for the conspiracy-themed night (a pyramid with an eye on the capstone). Each theme is a sketch with several presets to try:

| Theme | Sketch | Presets |
|---|---|---|
| The all-seeing eye | `eye` | watcher, dollar, reveal (opens on the drop), hypnotic, void |
| Sacred geometry | `sacred` | sierpinski, sierpinski-prism, flower-of-life, metatron, golden-spiral, sunflower, pyramid-tunnel, twisted-tunnel |
| Energy rising up the pyramid | `ascend` | charge, hieroglyph-wall, power-lines, full-power, cold |
| Red-string board | `field` | string-board, string-web, evidence-wall |
| Ciphers | `cipher` | pigpen, matrix-rain, numbers-station, novus-ordo |
| CCTV | `cctv` | night-vision, thermal-hunt, grey-cam, motion-alarm |
| Subliminal messages | `subliminal` | obey-flash, they-live, wake-up-strobe, drop-reveal, watching |
| Hypnosis | `rings` | hypno-spiral, mkultra, op-art, crop-rings |
| Aliens | `area51` | radar, radar-red, tractor-beam, abduction, crop-circle, crop-gold |
| Redacted files | `redacted` | top-secret, dark-files, heavy-redaction, declassified |
| Reptilians | `reptile` | lizard, snake-eye, iridescent, dragon |

Several of these react to the song's sections: the eye opens and the pyramid charges through a BUILD, and the DROP gives the reveal (eye wide open, words shown, message decoded, files declassified). Without showbrain the idle clock never reaches a BUILD or DROP, so those presets look quiet when testing at home.

### Shipped presets

Presets in `sketches/presets/NAME/*.json` ship with the sketch in git and show in the preset list alongside the ones saved on the brain. A preset file only needs the values it changes; everything else takes the sketch's defaults. Saving a preset with the same name on the brain overrides the shipped one.

### Text in sketches

Shaders can't draw text by themselves, so `tools/glsltext.py` writes a 5x7 pixel font and a list of messages into a sketch. The sketch lists its messages on a `// @messages: OBEY|CONSUME|WAKE UP` line and has an empty `// <text>` ... `// </text>` block; running `python3 brain/visuals/tools/glsltext.py brain/visuals/sketches/subliminal.glsl` fills the block. To change the words, edit the `@messages` line and run it again. The block gives the shader `textCov()` (a message), `charCov()` (one character), `msgLen()`, `msgChar()` and `CH_A` ... `CH_9` for drawing live numbers. Letters, digits, space and `: - . ! ? / # '` only.

## Max Cooper set

Simplified takes on five Max Cooper videos, each a sketch with presets:

| Video (artist) | Sketch | Presets |
|---|---|---|
| Seething (Andy Lomas) | `seething` | seething-red, brain, grey-mass, pink-coral |
| Seed (Vincent Houze) | `seed` | neon-grove, coral-bloom, blue-sprout, golden |
| Third (Vicetto) | `eye` | third-blue, third-green, third-teal |
| Harmonisch Serie (Whiskas fx) | `orb` | harmonisch, black-pearl, mirror, rgb-tiles |
| Echoes Reality (Graphset) | `pipes` | echoes, maze, round, blue-steel |

`emergence` (Order From Chaos, Maxime Causeret) is the sixth.
## The live track's waveform

Sketches can draw the song that's playing. rekordbox analyses every track when the USB is prepared, the decks share that colour waveform over Pro DJ Link, and deckdash already fetches it with the beat grid (`/api/wavedetail/N`, `/api/timeline/N`). Nothing has to be uploaded per song; it works for any track loaded from rekordbox media.

- `trackwave.py` in the visuals service follows showbrain's live deck. When its track changes (deckdash's `waveformKey`), it fetches the waveform and beat grid and resamples the waveform onto the grid, 8 samples per beat, keeping the loudest frame in each slice. It pushes the result to every page once per track as a `wave` event: RGBA bytes (height, bass, mids, highs) in a 256-wide texture.
- `render.js` uploads it as a texture and gives every sketch `vec4 wave(float beat)`: height, bass, mids and highs (0..1) at any beat of the track, where 1 is the first beat. Sketches look it up with `u_beat`, so it stays on the beat through tempo changes and can read ahead (`wave(u_beat + 16.0)` is four bars from now). Outside the track it returns 0.
- The `track` sketch uses it (terrain, scroll, ring, meters).
- **At home** (no decks) it plays a demo track, looped. To test with a real track, capture one on the rig with a track loaded: `python3 brain/visuals/tools/capture_wave.py http://<brain IP>:8080`. That saves `brain/visuals/state/wave-sample.*` (not in git), which is then used, looped, whenever no deck is live.
- `GET /api/wave` returns the current waveform message (`source`: `live`, `sample` or `demo`; `title`, `beats`, `spb`, `w`, `h`, `data`).
## The words you type

Sketches can't draw type by themselves, so the page draws it for them. There is a **Words** field
on the Visuals page and in the pad's drawer: type a few words separated by `|` and every sketch
can read them immediately.

- The service holds one string (`GET`/`POST` `/api/text`, up to 240 characters, control characters
  stripped) and pushes a `text` event to every page and projector.
- [`render.js`](../brain/projector/web/render.js) `setText()` splits it on `|` or a newline, takes
  the first eight words, and draws each into one row of a 2048×2048 eight-row atlas — each word
  scaled down to fit its row so the letterforms keep their proportions however long the word is.
  Drawn once per change on the CPU, uploaded as one texture. 2048 gives each row 256 pixels of
  height, which sounds generous until a sketch magnifies one row over half the screen: `wormhole`'s
  nearest ring does exactly that, and at 128 the diagonals of the letterforms stair-stepped.
- Every sketch gets `uniform sampler2D u_text`, `uniform float u_textn` (how many rows are in
  use) and the helper **`float word(vec2 uv, float row)`** in `COMMON`: coverage of word `row`
  at `uv`, where `uv` is 0..1 across that word's own row and `uv.y = 0` is the top of it. Off the
  edge of the word it returns 0, so a sketch can lay type anywhere without clipping it.
- The words are saved with the live values and go into presets, so a preset can carry its own
  message. `wormhole` is built on this; `subliminal`, `redacted` and `cipher` still use the older
  baked 5×7 font (`tools/glsltext.py`), which is compiled in and not editable live.

## Reaction-diffusion lab

**`http://sektor5.local:8110/rd.html`** (on Android, use the IP) is a standalone test page running a real Gray-Scott reaction-diffusion simulation on the GPU, after [Karl Sims](https://www.karlsims.com/rd.html). It is not a sketch: it's there to find looks and to check what the projector's GPU can handle before simulations go into the shared renderer.

- Pattern buttons set feed and kill (Coral, Mitosis, Mazes, Fingerprint, Worms, U-skate and more) and reseed. Draw with a finger or the mouse to add chemical.
- **Pattern map**: Uniform, Karl's f/k map (every behaviour at once), or Radial (your pattern in the middle, spots at the rim).
- Speed is in simulation steps per beat, so growth follows the tempo. **Seeds on beat** drops new growth on each beat (a burst on DROP); **Feed pulse** makes the pattern breathe with the kick. Beat comes from showbrain via `/api/events`, with a 120 BPM idle clock without it.
- The stats show fps, simulation size, and the storage the GPU supports (float32, float16, or an 8-bit packed fallback that works everywhere). If the fps drops, lower the resolution.
- URL options for bookmarking a look: `?preset=mazes&look=1&res=4&mode=2&speed=200&seeds=0.3&pulse=0&hud=0` (also `f=` and `k=`). **H** hides the panel.

## How it works

- `visuals.py` serves the control page, the sketch (`/api/sketch`) and its values (`/api/params`). It pushes `sketch` and `params` messages to every open page over Server-Sent Events (`/api/events`), plus showbrain's state for the preview's beat clock.
- The projector page and the mapping editor also connect to `:8110/api/events`. The renderer compiles the sketch as content `gen` and sets its `p_*` uniforms every frame, so slider moves need no recompile.
- The control page's preview is the projector's own renderer (`/render.js`, served from `../projector/web/`), so it shows exactly what the projector draws.
- The beat clock runs smoothly at the track's tempo and eases towards the show engine's reported position (at most 10% faster or slower), so network jitter on the ~20 updates a second doesn't show as stutter. It only jumps on a seek or track change.
- Shaders get `u_px` (one output pixel in surface units), so lines never go thinner than a pixel and don't shimmer as they move.
- Live values and presets are kept on the brain in `~/visuals/state/`, not in git.

## Speed

- **Compression and caching.** The visuals and projector services gzip what they send when the browser asks (pages and three.js shrink 3–4×, the venue 3×, and the Stage's light-frames stream 16×, each message still sent at once; the small event streams stay plain), and give every static file an ETag, so a browser that already has a file gets a 304 and no body. deckdash's HTTPS proxy passes neither header on, so it gets plain responses as before.
- **Adaptive resolution.** The previews (Visuals page, Live, the Launchpad, the Projection editor) draw at no more than 2× the screen's pixels, and `AutoRes` (in `render.js`) steps one down, to half at most, if the device can't hold ~45 fps, and back up when it can. A device that keeps up never changes; one held at 30 fps whatever it draws (Low Power Mode) is left at full.
- **Hidden pages pause.** Live, the Visuals page and the Launchpad close the event stream and stop polling while hidden (`pauseHidden`), and catch up the moment they're back. Live asks showbrain for its state 5 times a second on the Lights screen and twice a second on Visuals.

## API (on :8110)

`GET /api/events` (SSE: `sketch`, `params`, `state` ~20 times a second, which is showbrain's state without the lights' pixels, DMX, per-fixture detail and mixer, about 0.7 KB, and `wave` once per track; pages pass `pauseHidden` to `connectEvents` to close it while they're hidden, and it starts each connection with everything), `GET /api/wave`, `GET /api/sketch`, `GET /api/sketches`, `GET/POST /api/params` (POST any subset, values are clamped to their ranges), `POST /api/select {"sketch": NAME}`, `GET /api/presets`, `GET/POST /api/presets/NAME`, `POST /api/presets/NAME/load`.
